Blackwolf4183/Arduino_IMU_WAND/Project Report 2bc13acfc28a4a3c82e0ae88a6d2ab34/Render.png

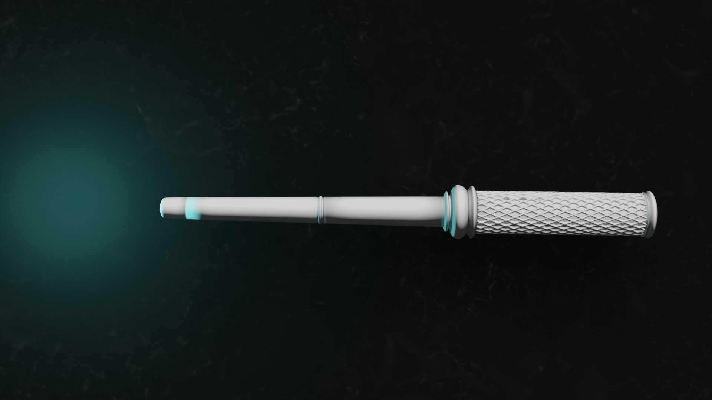
Project Report 2bc13acfc28a4a3c82e0ae88a6d2ab34/Render.png
