Blackwolf4183/Arduino_IMU_WAND/Local_testing/KMeansScript.py

# for loading/processing the images  
from tensorflow.keras.utils import load_img
from tensorflow.keras.utils import img_to_array
from keras.applications.vgg16 import preprocess_input 

# models 
from keras.applications.vgg16 import VGG16 
from keras.models import Model

# clustering and dimension reduction
from sklearn.cluster import KMeans
from sklearn.decomposition import PCA

# for everything else
import os
import numpy as np
import matplotlib.pyplot as plt
from random import randint
import pandas as pd
import pickle


path = r'C:\Users\apere\Desktop\Programming\Arduino\Arduino_IMU_WAND\Local_testing\dataset'
# change the working directory to the path where the images are located
os.chdir(path)

# this list holds all the image filename
spells = []

# creates a ScandirIterator aliased as files
with os.scandir(path) as files:
  # loops through each file in the directory
    for file in files:
        if file.name.endswith('.jpeg'):
          # adds only the image files to the flowers list
            spells.append(file.name)
            
            
            
model = VGG16()
model = Model(inputs = model.inputs, outputs = model.layers[-2].output)

def extract_features(file, model):
    # load the image as a 224x224 array
    img = load_img(file, target_size=(19,6))
    # convert from 'PIL.Image.Image' to numpy array
    img = np.array(img) 
    # reshape the data for the model reshape(num_of_samples, dim 1, dim 2, channels)
    reshaped_img = img.reshape(1,6,19,1) 
    # prepare image for model
    imgx = preprocess_input(reshaped_img)
    # get the feature vector
    features = model.predict(imgx, use_multiprocessing=True)
    return features

data = {}
p = r"C:\Users\apere\Desktop\Programming\Arduino\Arduino_IMU_WAND\Local_testing\feature_vectors"

# lop through each image in the dataset
for spell in spells:
    # try to extract the features and update the dictionary
    try:
        feat = extract_features(spell,model)
        data[spell] = feat
    # if something fails, save the extracted features as a pickle file (optional)
    except:
        with open(p,'wb') as file:
            pickle.dump(data,file)
          
 
# get a list of the filenames
filenames = np.array(list(data.keys()))
